JackGruber/esp32_ttn_environmental_sensor/src/lorawan.cpp

#include "lorawan.h"
#include "settings.h"
#include <hal/hal.h>
#include <SPI.h>
#include "io_pins.h"
#include "functions.h"
#include <power.h>
#include <particle.h>
#include <global.h>
#include <bme280.h>
#include <veml6075.h>
#include <tsl2591.h>

// Pin mapping
const lmic_pinmap lmic_pins = {
    .nss = PIN_LMIC_NSS,
    .rxtx = LMIC_UNUSED_PIN,
    .rst = PIN_LMIC_RST,
    .dio = {PIN_LMIC_DIO0, PIN_LMIC_DIO1, PIN_LMIC_DIO2},
};

static uint8_t LORA_DATA[15];

// Schedule TX every this many seconds (might become longer due to duty cycle limitations).
const unsigned TX_INTERVAL = LORA_TX_INTERVAL;

void os_getArtEui(u1_t *buf) { memcpy_P(buf, APPEUI, 8); }
void os_getDevEui(u1_t *buf) { memcpy_P(buf, DEVEUI, 8); }
void os_getDevKey(u1_t *buf) { memcpy_P(buf, APPKEY, 16); }

bool GO_DEEP_SLEEP = false;

RTC_DATA_ATTR lmic_t RTC_LMIC;

void LoRaWANSetup()
{
    Serial.println(F("LoRaWAN_Setup ..."));

    Serial.print(F("Saved seqnoUp: "));
    Serial.println(LMIC.seqnoUp);

    // LMIC init
    os_init();

    // Let LMIC compensate for +/- 1% clock error
    LMIC_setClockError(MAX_CLOCK_ERROR * 1 / 100);

    // Reset the MAC state. Session and pending data transfers will be discarded.
    LMIC_reset();

    if (RTC_LMIC.seqnoUp != 0)
    {
        LoraWANLoadLMICFromRTC();
    }

    // Start job
    LoraWANDo_send(&sendjob);
}

void LoraWANDo_send(osjob_t *j)
{
    // Check if there is not a current TX/RX job running
    if (LMIC.opmode & OP_TXRXPEND) {
        Serial.println(F("OP_TXRXPEND, not sending"));
    } else if (LMIC.opmode & OP_TXDATA) {
        Serial.println(F("OP_TXDATA, not sending"));
    } else {
        LoraWANGetData();

        // Prepare upstream data transmission at the next possible time.
        LMIC_setTxData2(1, LORA_DATA, sizeof(LORA_DATA), 0);
        Serial.println(F("Packet queued"));
    }
    // Next TX is scheduled after TX_COMPLETE event.
}

void onEvent(ev_t ev)
{
    Serial.print(os_getTime());
    Serial.print(": ");
    switch (ev)
    {
    case EV_SCAN_TIMEOUT:
        Serial.println(F("EV_SCAN_TIMEOUT"));
        break;
    case EV_BEACON_FOUND:
        Serial.println(F("EV_BEACON_FOUND"));
        break;
    case EV_BEACON_MISSED:
        Serial.println(F("EV_BEACON_MISSED"));
        break;
    case EV_BEACON_TRACKED:
        Serial.println(F("EV_BEACON_TRACKED"));
        break;
    case EV_JOINING:
        Serial.println(F("EV_JOINING"));
        break;
    case EV_JOINED:
        Serial.println(F("EV_JOINED"));
#ifndef DISABLE_JOIN
        {
            u4_t netid = 0;
            devaddr_t devaddr = 0;
            u1_t nwkKey[16];
            u1_t artKey[16];
            LMIC_getSessionKeys(&netid, &devaddr, nwkKey, artKey);
            Serial.print("netid: ");
            Serial.println(netid, DEC);
            Serial.print("devaddr: ");
            Serial.println(devaddr, HEX);
            Serial.print("artKey: ");
            for (size_t i = 0; i < sizeof(artKey); ++i)
            {
                Serial.print(artKey[i], HEX);
            }
            Serial.println("");
            Serial.print("nwkKey: ");
            for (size_t i = 0; i < sizeof(nwkKey); ++i)
            {
                Serial.print(nwkKey[i], HEX);
            }
            Serial.println("");
        }
        // Disable link check validation (automatically enabled
        // during join, but because slow data rates change max TX
        // size, we don't use it in this example.
        LMIC_setLinkCheckMode(0);
#endif
        break;
    /*
        || This event is defined but not used in the code. No
        || point in wasting codespace on it.
        ||
        || case EV_SCAN_FOUND:
        ||    Serial.println(F("EV_SCAN_FOUND"));
        ||    break;
        */
    case EV_JOIN_FAILED:
        Serial.println(F("EV_JOIN_FAILED"));
        break;
    case EV_REJOIN_FAILED:
        Serial.println(F("EV_REJOIN_FAILED"));
        break;
    case EV_TXCOMPLETE:
        Serial.println(F("EV_TXCOMPLETE"));

        if (LMIC.txrxFlags & TXRX_ACK)
        {
            Serial.println(F("Received ack"));
        }

        if (LMIC.dataLen)
        {
            Serial.print(LMIC.dataLen);
            Serial.println(F(" bytes of payload"));
        }

        GO_DEEP_SLEEP = true;

        break;
    case EV_LOST_TSYNC:
        Serial.println(F("EV_LOST_TSYNC"));
        break;
    case EV_RESET:
        Serial.println(F("EV_RESET"));
        break;
    case EV_RXCOMPLETE:
        // data received in ping slot
        Serial.println(F("EV_RXCOMPLETE"));
        break;
    case EV_LINK_DEAD:
        Serial.println(F("EV_LINK_DEAD"));
        break;
    case EV_LINK_ALIVE:
        Serial.println(F("EV_LINK_ALIVE"));
        break;
    /* This event is defined but not used in the code.
        case EV_SCAN_FOUND:
            DisplayPrintln(F("EV_SCAN_FOUND"), LORAWAN_STATE_DISPLAY_LINE);
            break;
        */
    case EV_TXSTART:
        Serial.println(F("EV_TXSTART"));
        break;
    case EV_TXCANCELED:
        Serial.println(F("EV_TXCANCELED"));
        break;
    case EV_RXSTART:
        /* do not print anything -- it wrecks timing */
        break;
    case EV_JOIN_TXCOMPLETE:
        Serial.println(F("EV_JOIN_TXCOMPLETE: no JoinAccept"));
        break;
    default:
        Serial.print(F("Unknown event: "));
        Serial.println((unsigned)ev);
        break;
    }
}

void LoraWANDo(void)
{
    long seconds = millis() / 1000;
    static unsigned long last_runntime_info = 0;
    static unsigned long runntime_info_ever_ms = 5000;

    if (GO_DEEP_SLEEP == true && !os_queryTimeCriticalJobs(ms2osticksRound((LORA_TX_INTERVAL * 1000))))
    {
        Serial.println(F("Go to DeepSleep ..."));
        Serial.print(F("Runtime was: "));
        Serial.print(seconds);
        Serial.println(F(" seconds"));

        LoraWANSaveLMICToRTC(LORA_TX_INTERVAL);
        Serial.flush();

        PowerDeepSleepTimer(LORA_TX_INTERVAL - 30 - 8); // 30sec for SDS011, 8 sec for remaining code 
    }
    else
    {
        if(last_runntime_info + runntime_info_ever_ms <  millis()) 
        { 
            Serial.print("Runtime: ");
            Serial.print(seconds);
            Serial.println(" seconds");
            #ifndef PRINTDEBUGS
                LoraWANDebug(LMIC);
            #endif
            last_runntime_info = millis();
        }

        os_runloop_once();
    }
}

/*
    Byte 1: VCC
    Byte 2: PM25
    Byte 3: PM25
    Byte 4: PM10
    Byte 5: PM10
    Byte 6: Temperature
    Byte 7: Temperature
    Byte 8: Humidity
    Byte 9: Pressure
    Byte 10: Pressure
    Byte 11: Pressure (first Bit), the remaining not used
    Byte 12: UV Index
    Byte 13: LUX (Value: 0-8800000)
    Byte 14: LUX
    Byte 15: LUX
*/
void LoraWANGetData()
{
    uint8_t tmp_u8;
    uint16_t tmp_u16;
    uint32_t tmp_u32;
    float tmp_float;

    // VCC
    /**************************************************************************/
    tmp_u8 = (ReadVBat() / 10) - 200;
    LORA_DATA[0] = tmp_u8;

    // PM25
    /**************************************************************************/
    tmp_u16 = (PM25 * 10);
    if (isnan(PM25))
    {
        LORA_DATA[1] = 255;
        LORA_DATA[2] = 255;
    }
    else
    {
        LORA_DATA[1] = tmp_u16 >> 8;
        LORA_DATA[2] = tmp_u16 & 0xFF;
    }

    // PM10
    /**************************************************************************/
    tmp_u16 = (PM10 * 10);
    if (isnan(PM10))
    {
        LORA_DATA[3] = 255;
        LORA_DATA[4] = 255;
    }
    else
    {
        LORA_DATA[3] = tmp_u16 >> 8;
        LORA_DATA[4] = tmp_u16 & 0xFF;
    }

    if(I2CCheckAddress(0x76))
    {
        // Temperature
        /**************************************************************************/
        tmp_u16 = (BME280ReadTemperature() * 10);
        LORA_DATA[5] = tmp_u16 >> 8;
        LORA_DATA[6] = tmp_u16 & 0xFF;

        // Humidity
        /**************************************************************************/
        tmp_float = BME280ReadHumidity();
        tmp_u8 = tmp_float;
        LORA_DATA[7] = tmp_u8;
        // Bit 8 for decimal 1 = 0.5
        if ((tmp_float - tmp_u8) > 0.251 && (tmp_float - tmp_u8) < 0.751)
        {
            LORA_DATA[7] |= (1 << 7);
        }
        else if ((tmp_float - tmp_u8) > 0.751)
        {
            LORA_DATA[7] = LORA_DATA[7] + 1;
        }

        // Pressure
        /**************************************************************************/
        tmp_float = BME280ReadPressure();
        tmp_u32 = (tmp_float * 100);
        LORA_DATA[8] = (tmp_u32 >> (8 * 0)) & 0xff;
        LORA_DATA[9] = (tmp_u32 >> (8 * 1)) & 0xff;
        LORA_DATA[10] = (tmp_u32 >> (8 * 2)) & 0xff;
    }
    else
    {
        LORA_DATA[5] = 255;
        LORA_DATA[6] = 255;
        LORA_DATA[7] = 255;
        LORA_DATA[8] = 255;
        LORA_DATA[9] = 255;
    }

    // UV Index
    if(I2CCheckAddress(0x10))
    {
        tmp_float = VEML6075GetUVI();
        tmp_u8 = (tmp_float * 10);
        LORA_DATA[11] = tmp_u8;
    }
    else
    {
        LORA_DATA[11] = 255;
    }

    // Lux
    if (I2CCheckAddress(0x29))
    {
        tmp_float = TSL2591GetLux(true, true);
        if(tmp_float < 0)
        {
            Serial.println("MAX LUX reached!");
            tmp_float = MAX_LUX;
        }
        tmp_u32 = tmp_float * 100;

        LORA_DATA[12] = (tmp_u32 >> (8 * 0)) & 0xff;
        LORA_DATA[13] = (tmp_u32 >> (8 * 1)) & 0xff;
        LORA_DATA[14] = (tmp_u32 >> (8 * 2)) & 0xff;
    }
    else
    {
        LORA_DATA[12] = 255;
        LORA_DATA[13] = 255;
        LORA_DATA[14] = 255;
    }
}

void LoraWANSaveLMICToRTC(int deepsleep_sec)
{
    Serial.println(F("Save LMIC to RTC ..."));
    RTC_LMIC = LMIC;

    //System time is resetted after sleep. So we need to calculate the dutycycle with a resetted system time
    unsigned long now = millis();

    // EU Like Bands
#if defined(CFG_LMIC_EU_like)
    for(int i = 0; i < MAX_BANDS; i++) {
        ostime_t correctedAvail = RTC_LMIC.bands[i].avail - ((now/1000.0 + deepsleep_sec ) * OSTICKS_PER_SEC);
        if(correctedAvail < 0) {
            correctedAvail = 0;
        }
        RTC_LMIC.bands[i].avail = correctedAvail;
    }

    RTC_LMIC.globalDutyAvail = RTC_LMIC.globalDutyAvail - ((now/1000.0 + deepsleep_sec ) * OSTICKS_PER_SEC);
    if(RTC_LMIC.globalDutyAvail < 0) 
    {
        RTC_LMIC.globalDutyAvail = 0;
    }
#else
    Serial.println("No DutyCycle recalculation function!")
#endif

    #ifndef PRINTDEBUGS
        LoraWANDebug(RTC_LMIC);
    #endif
}

void LoraWANLoadLMICFromRTC()
{
    Serial.println(F("Load LMIC vars from RTC ..."));
    LMIC = RTC_LMIC;

    #ifndef PRINTDEBUGS
        LoraWANDebug(RTC_LMIC);
    #endif
}

void LoraWANPrintVersion(void)
{
    Serial.print(F("LMIC Version: "));
    Serial.print(ARDUINO_LMIC_VERSION_GET_MAJOR (ARDUINO_LMIC_VERSION) );
    Serial.print(F("."));
    Serial.print(ARDUINO_LMIC_VERSION_GET_MINOR (ARDUINO_LMIC_VERSION) );
    Serial.print(F("."));
    Serial.print(ARDUINO_LMIC_VERSION_GET_PATCH (ARDUINO_LMIC_VERSION) );
    Serial.print(F("."));
    Serial.println(ARDUINO_LMIC_VERSION_GET_LOCAL (ARDUINO_LMIC_VERSION) );  
}

// opmode def 
// https://github.com/mcci-catena/arduino-lmic/blob/89c28c5888338f8fc851851bb64968f2a493462f/src/lmic/lmic.h#L233
void LoraWANPrintLMICOpmode(void)
{
    Serial.print(F("LMIC.opmode: "));
    if (LMIC.opmode & OP_NONE) { Serial.print(F("OP_NONE ")); }
    if (LMIC.opmode & OP_SCAN) { Serial.print(F("OP_SCAN ")); }
    if (LMIC.opmode & OP_TRACK) { Serial.print(F("OP_TRACK ")); }
    if (LMIC.opmode & OP_JOINING) { Serial.print(F("OP_JOINING ")); }
    if (LMIC.opmode & OP_TXDATA) { Serial.print(F("OP_TXDATA ")); }
    if (LMIC.opmode & OP_POLL) { Serial.print(F("OP_POLL ")); }
    if (LMIC.opmode & OP_REJOIN) { Serial.print(F("OP_REJOIN ")); }
    if (LMIC.opmode & OP_SHUTDOWN) { Serial.print(F("OP_SHUTDOWN ")); }
    if (LMIC.opmode & OP_TXRXPEND) { Serial.print(F("OP_TXRXPEND ")); }
    if (LMIC.opmode & OP_RNDTX) { Serial.print(F("OP_RNDTX ")); }
    if (LMIC.opmode & OP_PINGINI) { Serial.print(F("OP_PINGINI ")); }
    if (LMIC.opmode & OP_PINGABLE) { Serial.print(F("OP_PINGABLE ")); }
    if (LMIC.opmode & OP_NEXTCHNL) { Serial.print(F("OP_NEXTCHNL ")); }
    if (LMIC.opmode & OP_LINKDEAD) { Serial.print(F("OP_LINKDEAD ")); }
    if (LMIC.opmode & OP_LINKDEAD) { Serial.print(F("OP_LINKDEAD ")); }
    if (LMIC.opmode & OP_TESTMODE) { Serial.print(F("OP_TESTMODE ")); }
    if (LMIC.opmode & OP_UNJOIN) { Serial.print(F("OP_UNJOIN ")); }
    Serial.println("");
}

void LoraWANDebug(lmic_t lmic_to_check)
{
    Serial.println("");
    Serial.println("");
    
    LoraWANPrintLMICOpmode();

    Serial.print("LMIC.seqnoUp = ");
    Serial.println(lmic_to_check.seqnoUp); 

    Serial.print("LMIC.globalDutyRate = ");
    Serial.print(lmic_to_check.globalDutyRate);
    Serial.print(" osTicks, ");
    Serial.print(osticks2ms(lmic_to_check.globalDutyRate)/1000);
    Serial.println(" sec");

    Serial.print("LMIC.globalDutyAvail = ");
    Serial.print(lmic_to_check.globalDutyAvail);
    Serial.print(" osTicks, ");
    Serial.print(osticks2ms(lmic_to_check.globalDutyAvail)/1000);
    Serial.println(" sec");

    Serial.print("LMICbandplan_nextTx = ");
    Serial.print(LMICbandplan_nextTx(os_getTime()));
    Serial.print(" osTicks, ");
    Serial.print(osticks2ms(LMICbandplan_nextTx(os_getTime()))/1000);
    Serial.println(" sec");

    Serial.print("os_getTime = ");
    Serial.print(os_getTime());
    Serial.print(" osTicks, ");
    Serial.print(osticks2ms(os_getTime()) / 1000);
    Serial.println(" sec");

    Serial.print("LMIC.txend = ");
    Serial.println(lmic_to_check.txend);
    Serial.print("LMIC.txChnl = ");
    Serial.println(lmic_to_check.txChnl);

    Serial.println("Band \tavail \t\tavail_sec\tlastchnl \ttxcap");
    for (u1_t bi = 0; bi < MAX_BANDS; bi++)
    {
        Serial.print(bi);
        Serial.print("\t");
        Serial.print(lmic_to_check.bands[bi].avail);
        Serial.print("\t\t");
        Serial.print(osticks2ms(lmic_to_check.bands[bi].avail)/1000);
        Serial.print("\t\t");
        Serial.print(lmic_to_check.bands[bi].lastchnl);
        Serial.print("\t\t");
        Serial.println(lmic_to_check.bands[bi].txcap);
        
    }
    Serial.println("");
    Serial.println("");
}
