JackGruber/esp32_ttn_environmental_sensor/include/settings.h

#define LORA_TX_INTERVAL 300
#define LMIC_LORA_SF  DR_SF7 // LORA Data rate
#define SDS011_SERIAL Serial2 // Pin 16/17
#define REF_VCCRAW_ESP32 931 // VCCraw read from ESP32
#define REF_VBAT 3496 // Voltage in mV at battery
#define MAX_LUX 88001 // Value that is sent when the maximum LUX value is reached that the sensor supports. (Output from the lib is in this case -1)
#define PRINTDEBUGS
