JackGruber/esp32_ttn_environmental_sensor/src/functions.h

#pragma once
#ifndef _FUNCTIONS_H
#define _FUNCTIONS_H

#include <Arduino.h>

void PrintResetReason(void);
void SetupPins();
long ReadVBat();
void I2CScanner(void);
bool I2CCheckAddress(byte);

#endif
